droyktton/medidorCO2/medidoresIB/doc/20210531_194427.jpg

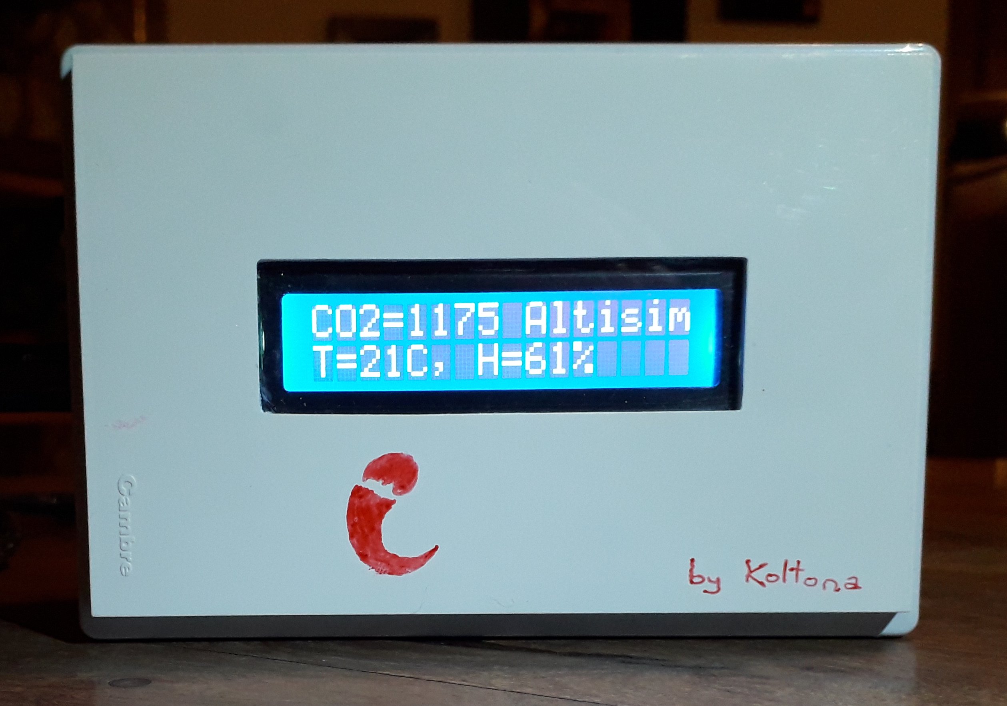
medidoresIB/doc/20210531_194427.jpg
