droyktton/medidorCO2/medidoresIB/doc/ach2ppm.png

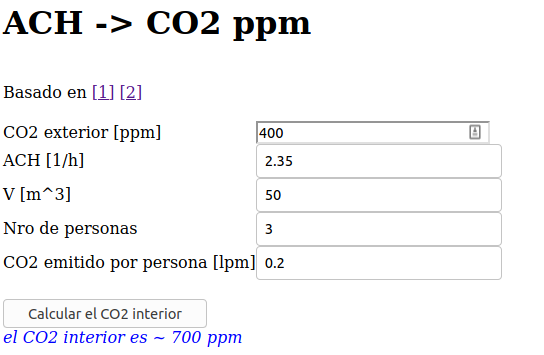
medidoresIB/doc/ach2ppm.png
