droyktton/medidorCO2/medidoresIB/doc/publicMonitor.png

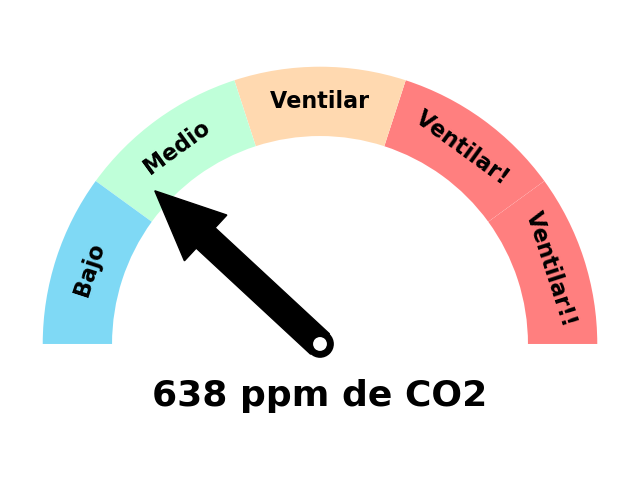
medidoresIB/doc/publicMonitor.png
